matiasrg/FdD_Equipo_04/Proyecto/MóduloMecánico/vfinal/Bocetos/Boceto interior VFINAL.pdf

## BOCETO - EcoAlerta

Equipo 04 - Fundamentos de Diseño

DIBUJADO POR:
- Palacios Ochoa Jose Elias
- Jimenez Ayala Cielo Saori
- Espinoza Mayta Adriana
- Santos Almonte Jesilin

VISTA INTERNA:

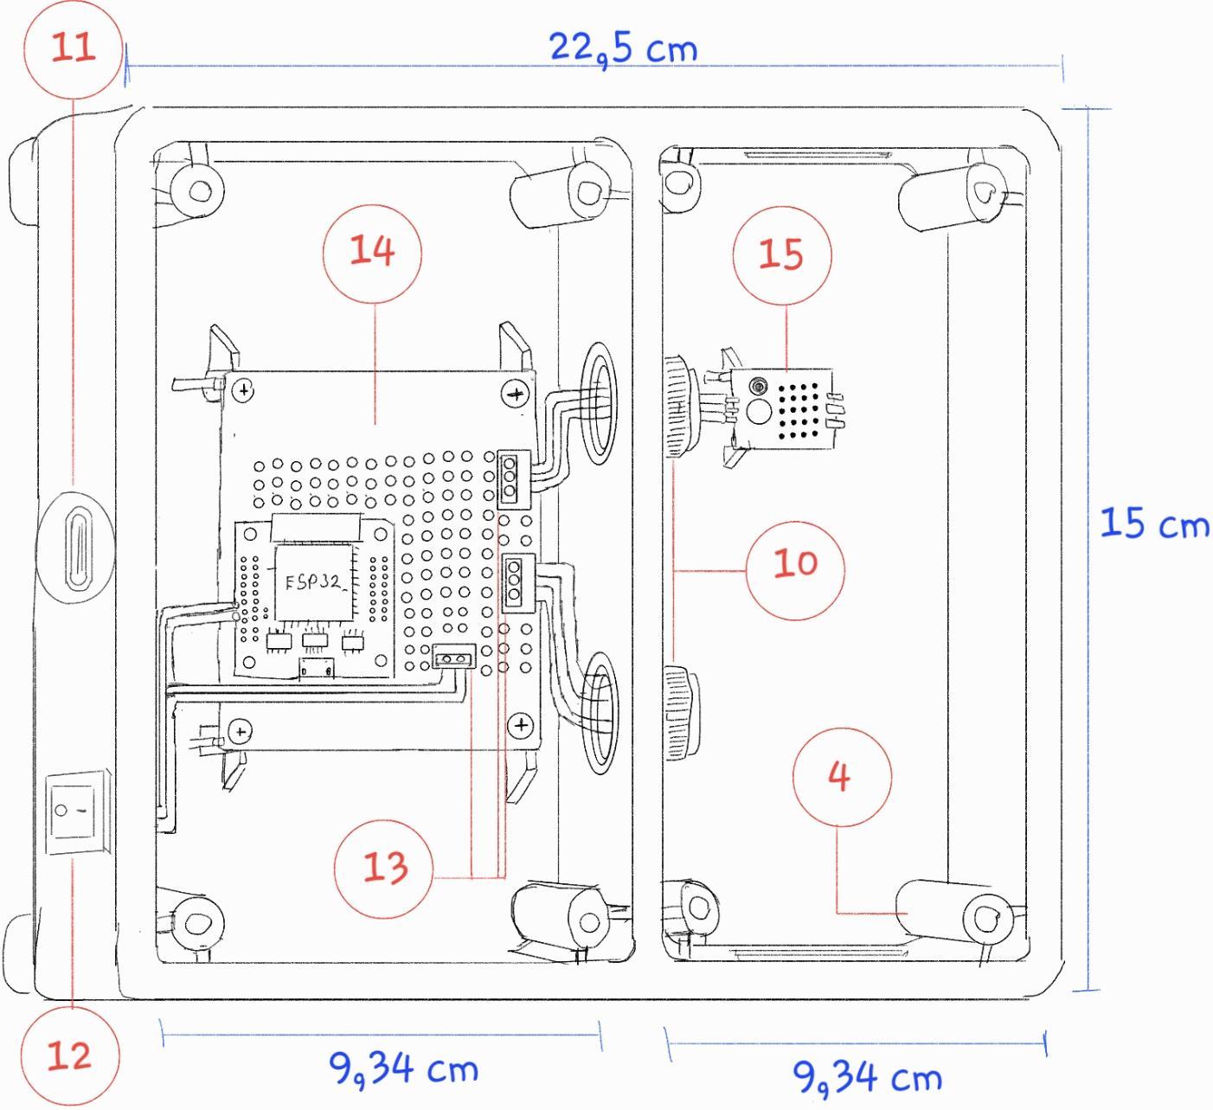
[picture p30: figure]

Descripción del funcionamiento: | LISTA DE DESPIECE:

La vista interna permite observar la organización de los componentes electrónicos dentro de la carcasa. Se identifican el

PIEZA | NOMBRE

microcontrolador ESP32, la bornera, el interruptor de encendido, el conector USB Tipo-C y los elementos de soporte que facilitan el montaje y
funcionamiento seguro del
sistema.
④ | Base/apoyo para tapa
⑩ | Prensaestopa PG7
⑪ | Conector USB Tipo-C hembra para montaje en panel
⑫ | Interruptor de encendido/apagado (ON/OFF)
⑬ | Bornera
⑭ | Microcontrolador ESP32 y placa perforada
⑮ | Sensor de temperatura y humedad (DHT22)
