matiasrg/FdD_Equipo_04/Proyecto/MóduloMecánico/vfinal/Bocetos/Boceto isométrico VFINAL.pdf

## BOCETO - EcoAlerta

Equipo 04 - Fundamentos de Diseño

DIBUJADO POR:
- Palacios Ochoa Jose Elias
- Jimenez Ayala Cielo Saori
- Espinoza Mayta Adriana
- Santos Almonte Jesilin
VISTA ISOMÉTRICA

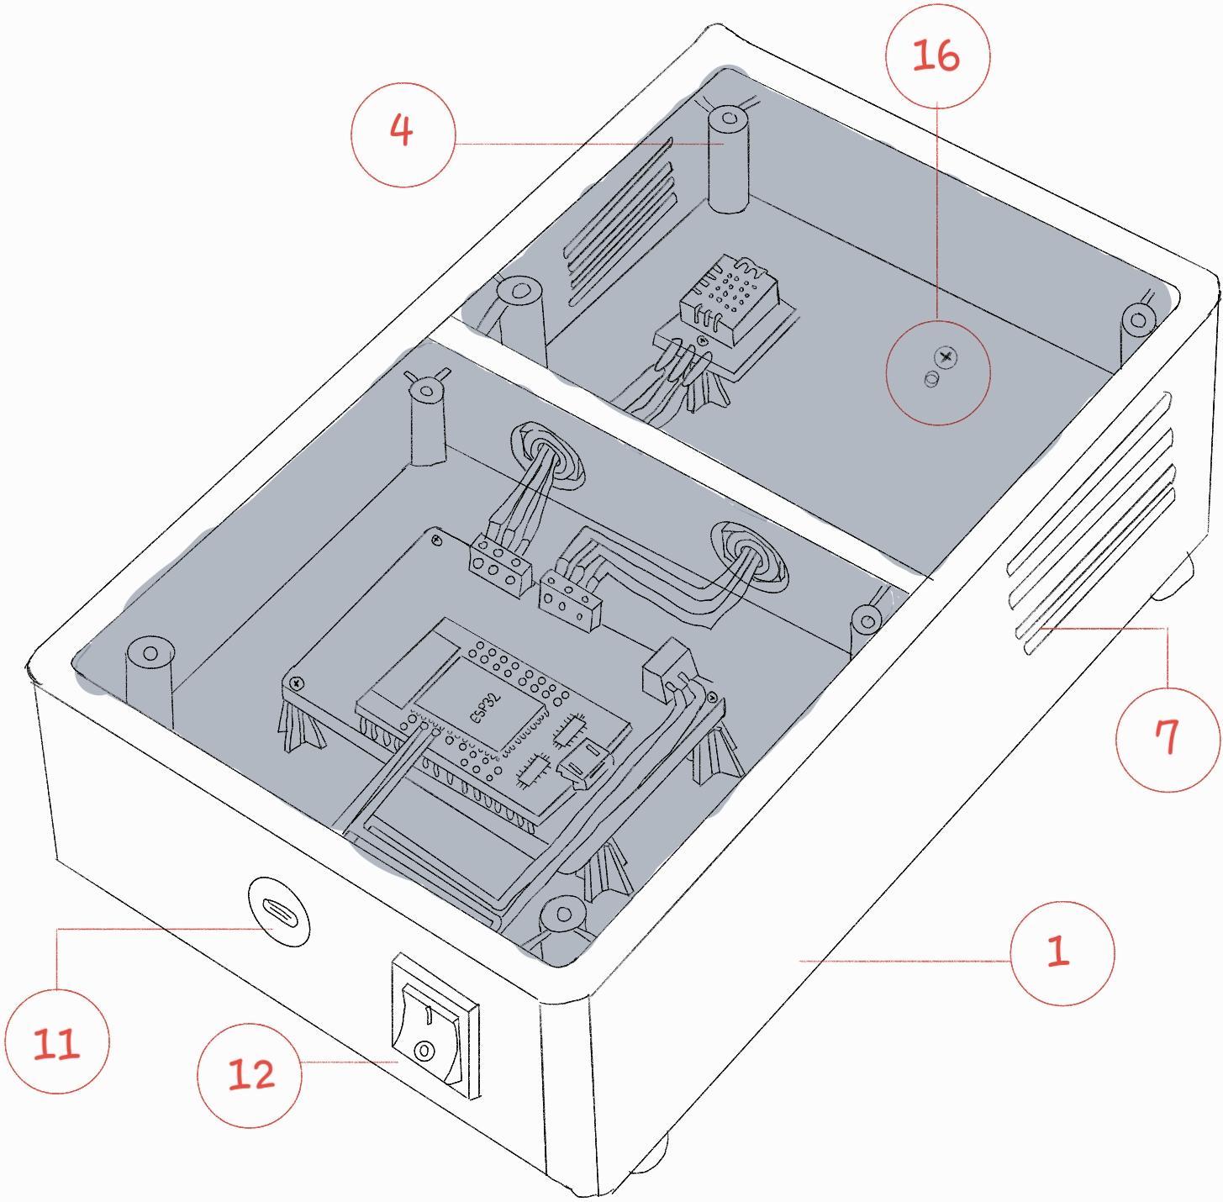
[picture p31: figure]

Descripción del funcionamiento: | LISTA DE DESPIECE:

La vista isométrica ofrece una representación tridimensional del dispositivo ensamblado, permitiendo visualizar

PIEZA | NOMBRE

simultáneamente varias caras de la estructura. Se aprecian la carcasa principal, las rejillas de ventilación, el sensor UV y los elementos de conexión externa, proporcionando una visión general del diseño final del producto.

① | Carcasa exterior rectangular (base)
④ | Base/apoyo para tapa
⑦ | Rejillas de ventilación lineales
⑪ | Conector USB Tipo-C hembra para montaje en panel
⑫ | Interruptor de encendido/apagado (ON/OFF)
⑯ | Sensor UV (UV SENS)
