matiasrg/FdD_Equipo_04/Proyecto/MóduloMecánico/vfinal/Bocetos/Boceto tapas VFINAL.pdf

## BOCETO - EcoAlerta

Equipo 04 - Fundamentos de Diseño

DIBUJADO POR:
- Palacios Ochoa Jose Elias
- Jimenez Ayala Cielo Saori
- Espinoza Mayta Adriana
- Santos Almonte Jesilin

VISTA DE TAPAS

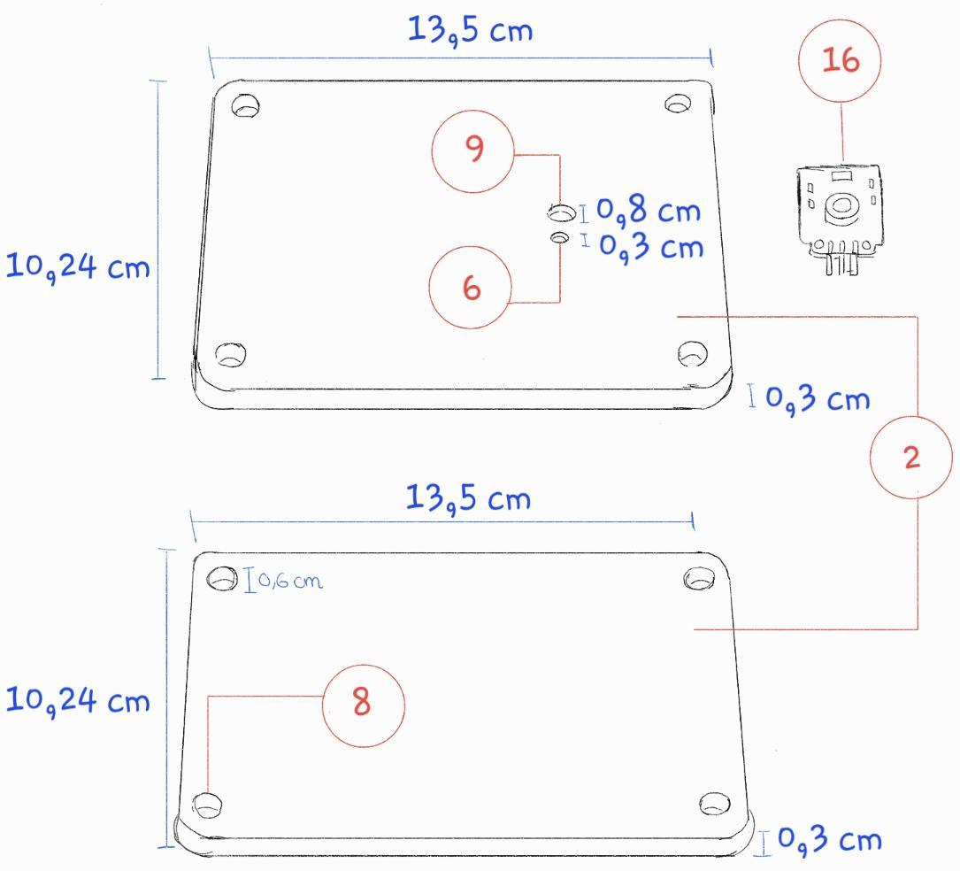
[picture p32: figure]

Descripción del funcionamiento: | LISTA DE DESPIECE:

Esta vista destaca la tapa superior del dispositivo y los elementos asociados a la medición de radiación ultravioleta. Se observa

PIEZA | NOMBRE

la abertura destinada al sensor UV junto con su soporte de fijación, así como los orificios para el ensamblaje mediante un tornillo que asegura la unión con la tapa y la carcasa que veremos más adelante.

② | Tapa protectora
⑥ | Apertura circular y soporte para sensor UV
⑧ | Hueco para tornillo
⑨ | Hueco para sensor UV
⑯ | Sensor UV (UV SENS)
