matiasrg/FdD_Equipo_04/Proyecto/MóduloMecánico/vfinal/Bocetos/Boceto conjunto VFINAL.pdf

## BOCETO - EcoAlerta

Equipo 04 - Fundamentos de Diseño

DIBUJADO POR:
- Palacios Ochoa Jose Elias
- Jimenez Ayala Cielo Saori
- Espinoza Mayta Adriana
- Santos Almonte Jesilin

BOCETO EN CONJUNTO

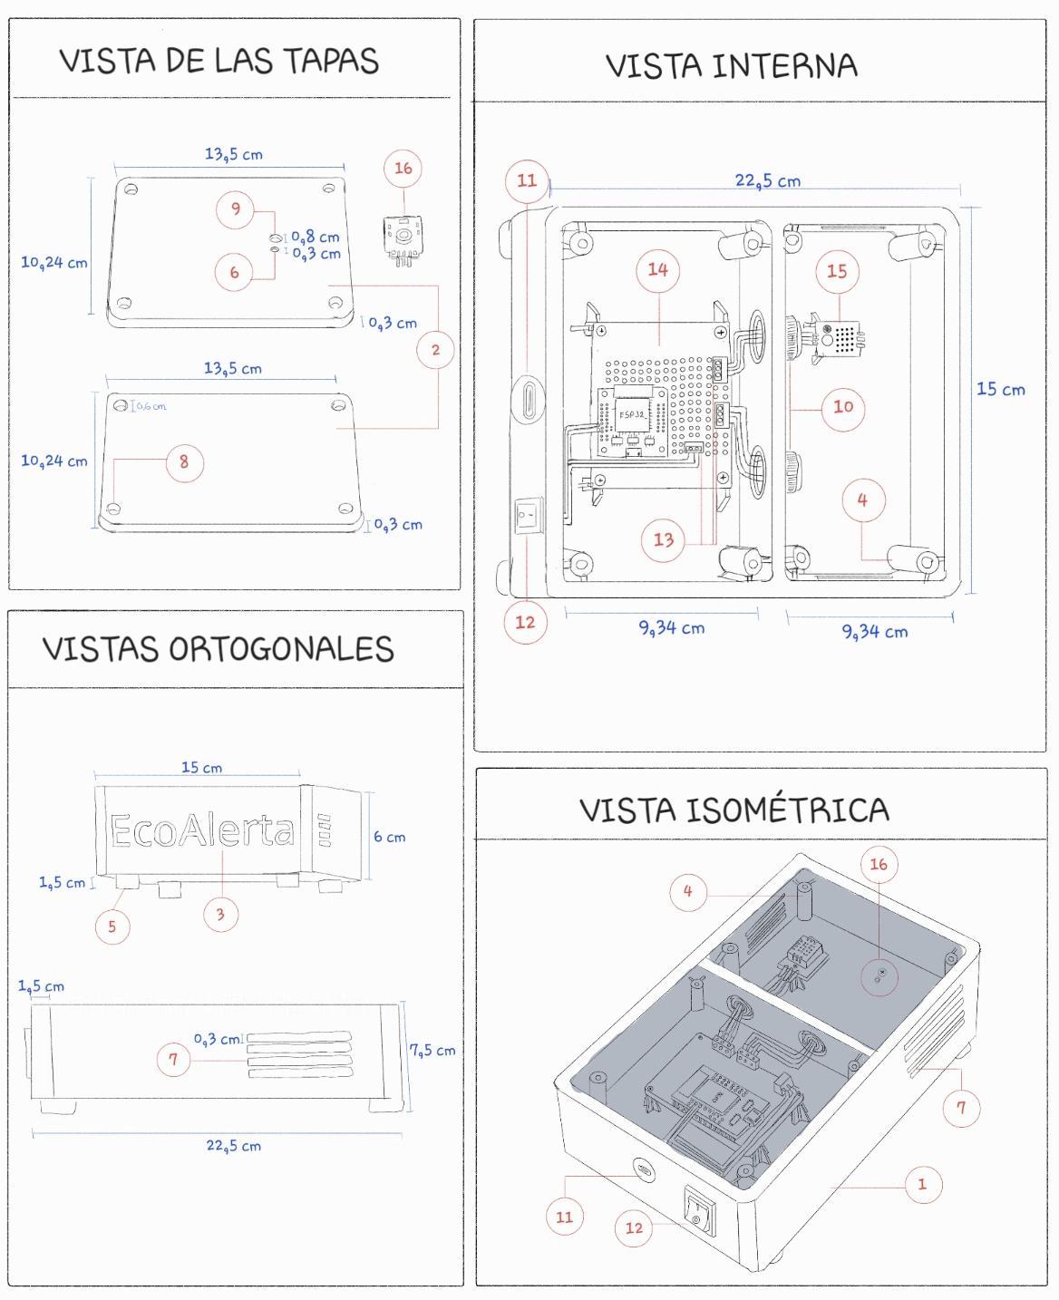
[picture p33: figure]

Descripción del funcionamiento: LISTA DE DESPIECE:

El dispositivo presenta una carcasa
rectangular compacta diseñada para
uso en exteriores. En la parte
superior se observan el sensor UV, colocado en una abertura circular para recibir directamente la radiación solar, y el sensor DHT22 junto a rejillas lineales que permiten la circulación de aire. En el interior se ubica el módulo ESP32 con las conexiones electrónicas, mientras que en el panel frontal se integran el puerto USB Tipo-C, el interruptor de encendido y el logotipo del proyecto EcoAlerta. El diseño busca facilitar tanto el monitoreo ambiental como el acceso para mantenimiento y alimentación eléctrica.
PIEZA | NOMBRE | MATERIAL
① | Carcasa exterior rectangular (base) | PETG
② | Tapa protectora | PETG
③ | Panel frontal con logo | PETG
④ | Base/apoyo para tapa | PETG
⑤ | Patitas | PETG
⑥ | Apertura circular y soporte para sensor UV | PETG
⑦ | Rejillas de ventilación lineales | PETG
⑧ | Hueco para tornillo | Integrado en la tapa
⑨ | Hueco para sensor UV | Integrado en la tapa
⑩ | Prensaestopa PG7 | Nylon (PA66)
⑪ | Conector USB Tipo-C hembra para montaje en panel | Componente electrónico
⑫ | Interruptor de encendido/apagado (ON/OFF) | Componente electrónico
⑬ | Bornera | Componente electrónico
⑭ | Microcontrolador ESP32 y placa perforada | Componentes electrónicos
⑮ | Sensor de temperatura y humedad (DHT22) | Componente electrónico
⑯ | Sensor UV (UV SENS) | Componente electrónico
