matiasrg/FdD_Equipo_04/Proyecto/MóduloMecánico/Certificados/Jose Palacios/Jose Palacios.pdf

JOSE ELIAS PALACIOS OCHOA

Advanced Onshape Assemblies

May 21, 2026

JOSE ELIAS PALACIOS OCHOA

April 29, 2026

Introduction to Onshape Assemblies

JOSE ELIAS PALACIOS OCHOA

April 29, 2026

Detailed Drawings

JOSE ELIAS PALACIOS OCHOA

April 30, 2026

Introduction to Drawings

JOSE ELIAS PALACIOS OCHOA

Introduction to Part Studios

April 29, 2026

JOSE ELIAS PALACIOS OCHOA

Introduction to Sketching

April 29, 2026
