matiasrg/FdD_Equipo_04/Proyecto/MóduloMecánico/Certificados/Adriana Espinoza/Adriana Espinoza.pdf

Adriana Anghely Espinoza Mayta

Advanced Onshape Assemblies

May 21, 2026

Adriana Anghely Espinoza Mayta

April 30, 2026

Detailed Drawings

Adriana Anghely Espinoza Mayta

April 30, 2026

Introduction to Drawings

Adriana Anghely Espinoza Mayta

April 30, 2026

Introduction to Onshape Assemblies

Adriana Anghely Espinoza Mayta

Introduction to Part Studios

April 30, 2026

Adriana Anghely Espinoza Mayta

Introduction to Sketching

April 30, 2026
