matiasrg/FdD_Equipo_04/Proyecto/MóduloMecánico/Certificados/Cielo Jiménez/Saori Jimenez.pdf

Cielo Saori Jimenez Ayala

Advanced Onshape Assemblies

May 21, 2026

Cielo Saori Jimenez Ayala

April 30, 2026

Detailed Drawings

Cielo Saori Jimenez Ayala

April 30, 2026

Introduction to Drawings

Cielo Saori Jimenez Ayala

April 30, 2026

Introduction to Onshape Assemblies

Cielo Saori Jimenez Ayala

Introduction to Part Studios

April 30, 2026

Cielo Saori Jimenez Ayala

Introduction to Sketching

April 30, 2026
