matiasrg/FdD_Equipo_04/Proyecto/MóduloMecánico/Certificados/Jesilin Santos/Jesilin Santos.pdf

Jesilin Santos Almonte

Advanced Onshape Assemblies

May 21, 2026

Jesilin Santos Almonte

April 29, 2026

Detailed Drawings

Jesilin Santos Almonte

April 30, 2026

Introduction to Drawings

Jesilin Santos Almonte

April 29, 2026

Introduction to Onshape Assemblies

Jesilin Santos Almonte

Introduction to Part Studios

April 29, 2026

Jesilin Santos Almonte

Introduction to Sketching

April 29, 2026
