matiasrg/FdD_Equipo_04/Proyecto/MóduloMecánico/Certificados/Matias Rivera/Matias Rivera.pdf

Matias Rivera

Advanced Onshape Assemblies

May 21, 2026

MatiasR Rivera

April 30, 2026

Detailed Drawings

MatiasR Rivera

April 30, 2026

Introduction to Drawings

MatiasR Rivera

April 30, 2026

Introduction to Onshape Assemblies

MatiasR Rivera

Introduction to Part Studios

April 30, 2026

MatiasR Rivera

Introduction to Sketching

April 30, 2026
