matiasrg/FdD_Equipo_04/FundDiseño/Talleres/Taller_04/Taller_04.md

# LISTA DE PATENTES:

1. **UV light monitoring system for a UV decontamination apparatus**
   -Resumen: Esta patente describe un sistema de monitoreo de luz ultravioleta (UV) aplicado a dispositivos de desinfección. El sistema es capaz de estimar con precisión la irradiancia UV que recibe una superficie, incluso cuando esta se encuentra en diferentes ángulos respecto a la fuente de luz UV.
   <br>
   -Código: US12409241B2
   <br>
   -link: https://worldwide.espacenet.com/patent/search/family/073196745/publication/US12409241B2?q=pn%3DUS12409241B2
   <br>
   -Imagen:
   <br>
   <div align="center">
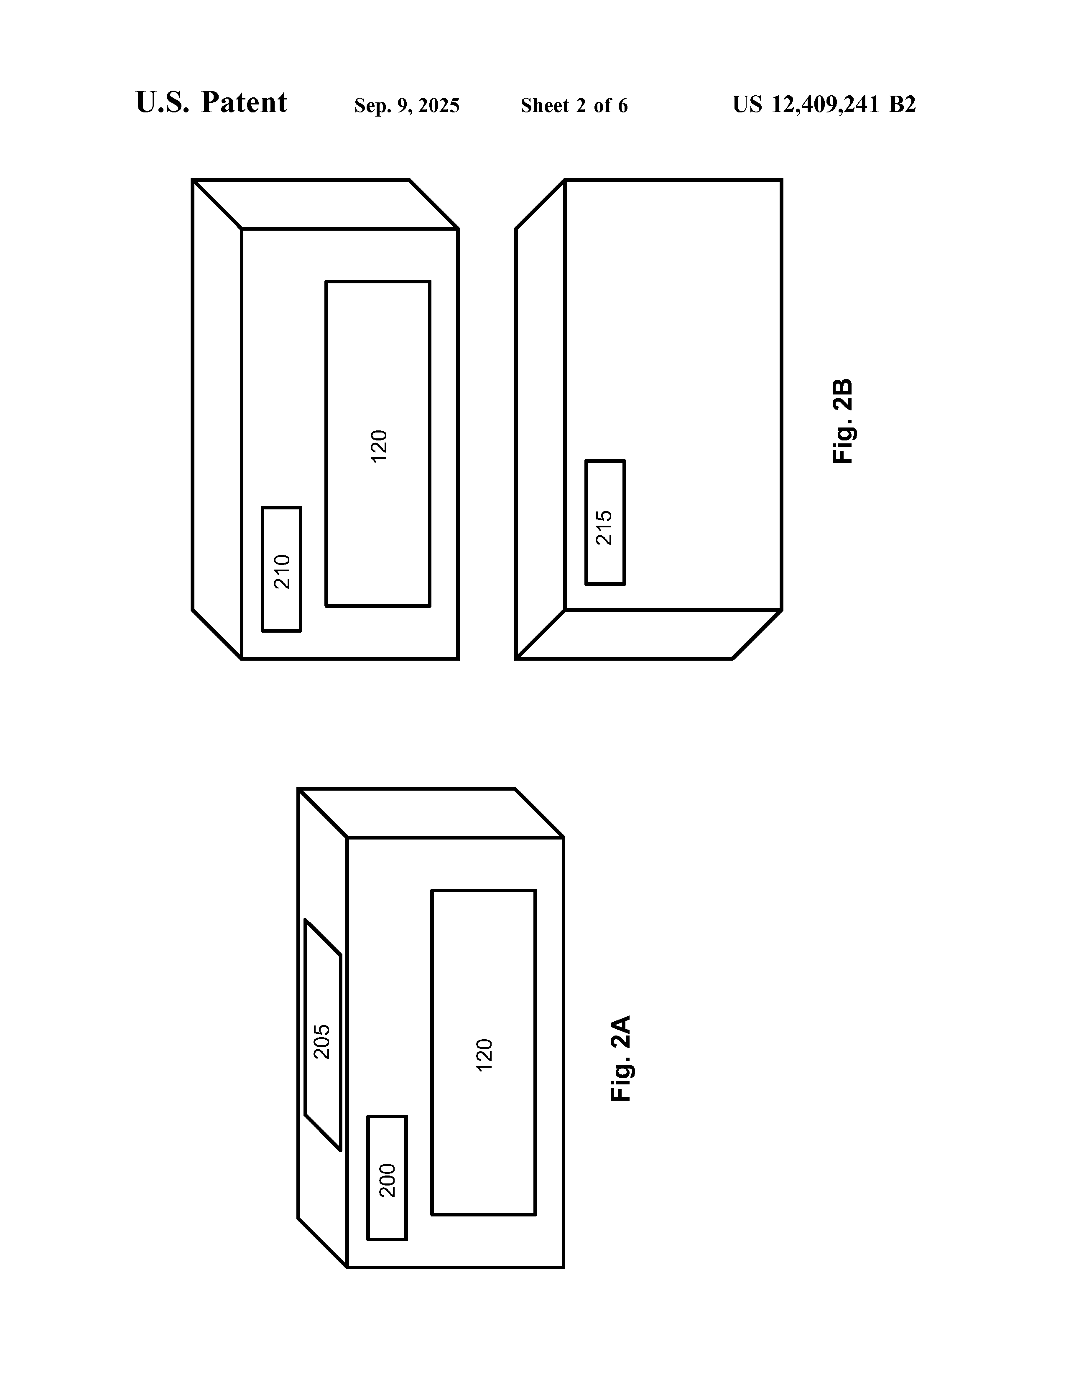
[picture p34: Recursos/Imágenes/patente1.png]
      
   </div>
   <br>
2. **Sistema de gestión de inventarios basado en inteligencia artificial para monitorear la disponibilidad de productos mediante datos IoT**
   (KI-gestütztes Bestandsverwaltungssystem zur Überwachung der Produktverfügbarkeit mithilfe von IoT-Daten)
   
  -Resumen: Esta patente describe un sistema de gestión de inventarios basado en Internet de las Cosas (IoT) e inteligencia artificial (IA), diseñado para monitorear la disponibilidad de productos en tiempo real dentro de entornos como almacenes o tiendas
  <br>
  -Código: DE202025101045U1
  <br>
  -Link: https://worldwide.espacenet.com/patent/search/family/095158102/publication/DE202025101045U1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
  <br>
  -Imagen:
  <br>
   <div align="center">
      
   </div>

3. **Sistema, dispositivo y métodos para el seguimiento de la exposición a la luz**
    (Light exposure tracking system, device, and methods)
   -Resumen: La patente describe un sistema portátil (wearable) que mide la exposición a la radiación UV en tiempo real. El dispositivo recopila datos y los envía a un sistema externo que calcula el índice UV y la dosis acumulada diaria, ayudando a prevenir riesgos para la salud
   <br>
   -Código: US11579015B2
   <br>
   -Link: https://worldwide.espacenet.com/patent/search/family/065362927/publication/US11579015B2?q=pn%3DUS11579015B2
   <br>
   -Imágen:
    <div align="center">
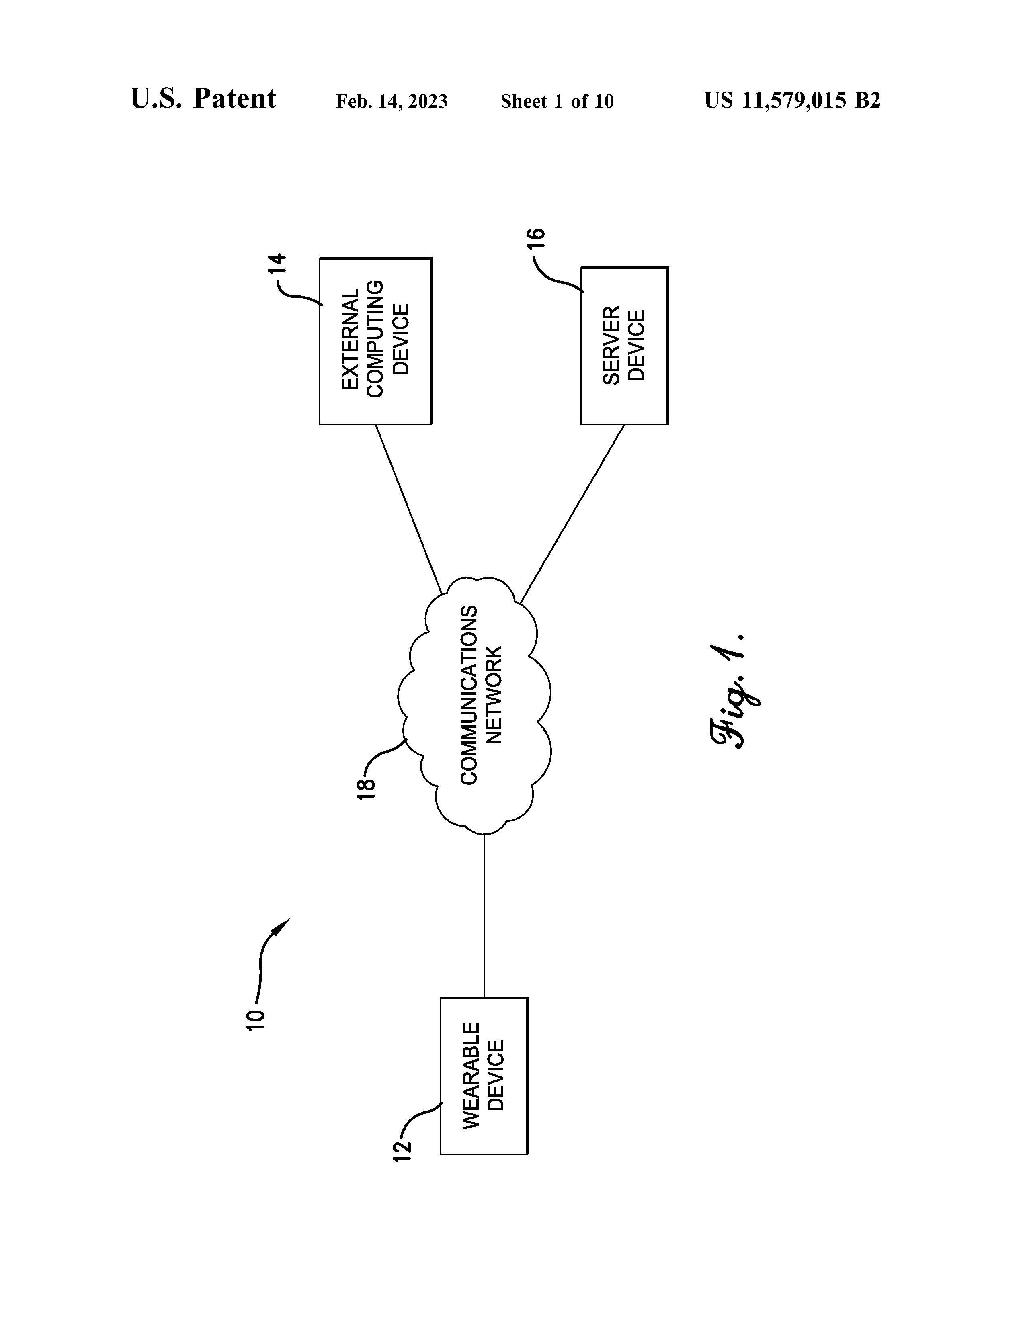
[picture p35: Recursos/Imágenes/patente3.png]
      
   </div>
