matiasrg/FdD_Equipo_04/FundDiseño/Talleres/taller_10/onshape/Imagen - Modelado 3D.pdf

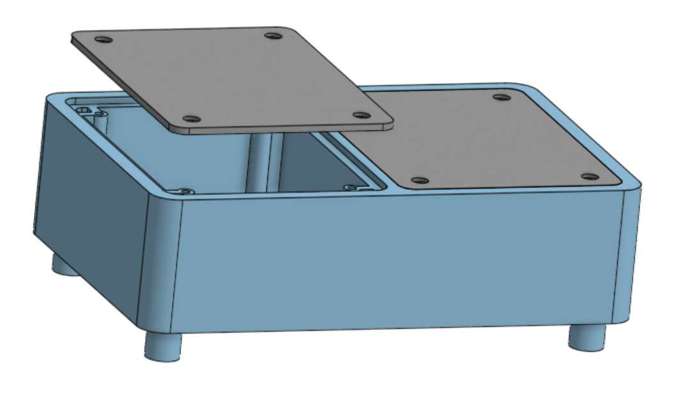
[picture p38: page 1]
