matiasrg/FdD_Equipo_04/Recursos/Productos comerciales/Brochure producto 2.pdf

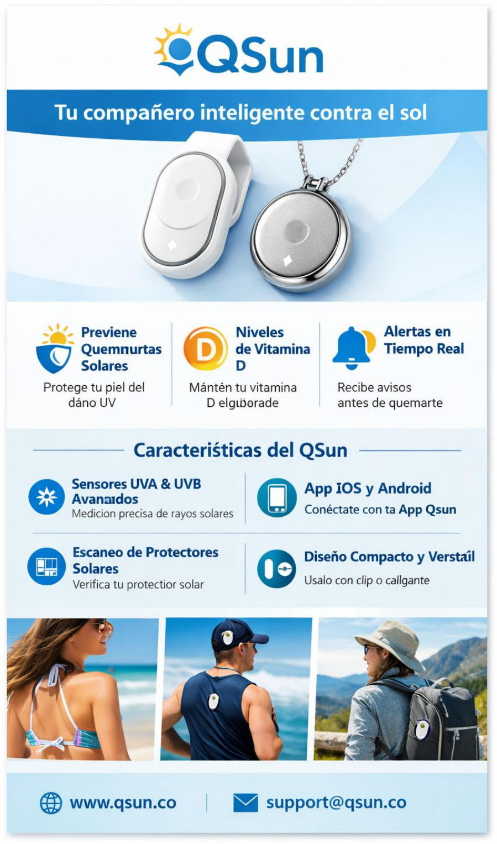
[picture p39: page 1]
