matiasrg/FdD_Equipo_04/Proyecto/MóduloMecánico/vfinal/Bocetos/Boceto Frontal y Lateral VFINAL.pdf

## BOCETO - EcoAlerta

Equipo 04 - Fundamentos de Diseño

DIBUJADO POR:
- Palacios Ochoa Jose Elias
- Jimenez Ayala Cielo Saori
- Espinoza Mayta Adriana
- Santos Almonte Jesilin

VISTAS ORTOGONALES

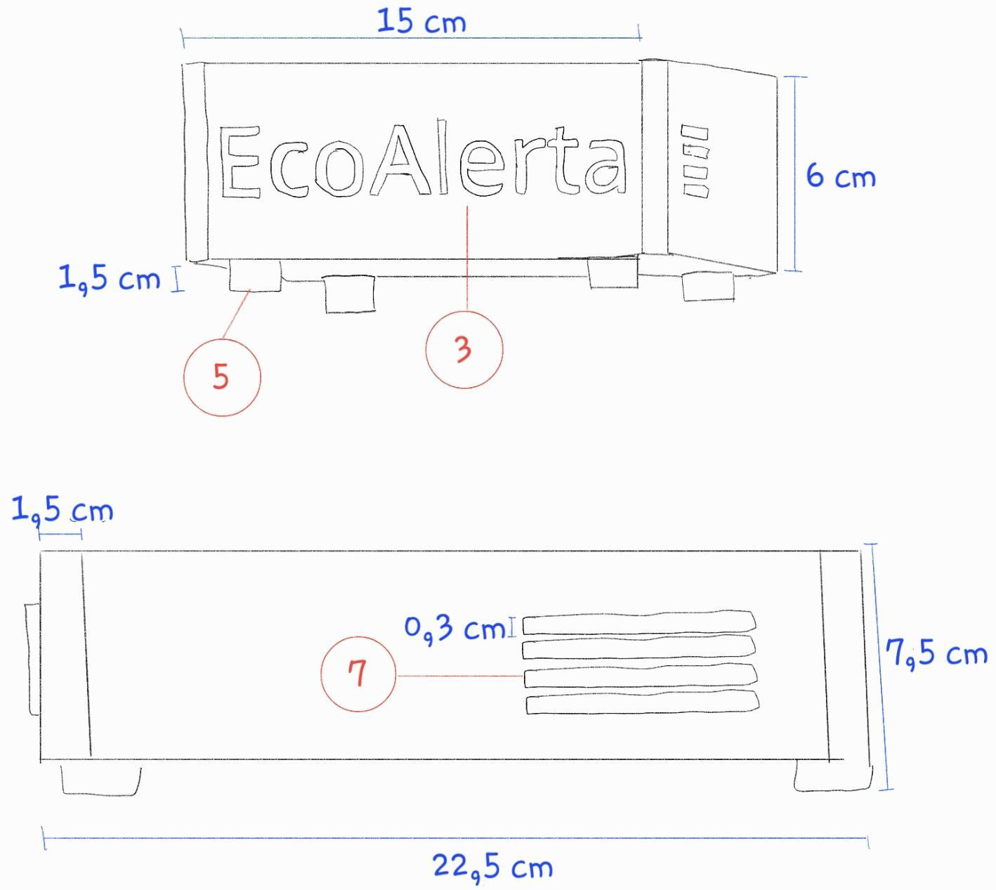
[picture p40: figure]

Descripción del funcionamiento: | LISTA DE DESPIECE:

Las vistas ortogonales presentan el dispositivo desde diferentes perspectivas, permitiendo apreciar con mayor claridad su forma,

PIEZA | NOMBRE

dimensiones y distribución exterior. En ellas destacan las rejillas de ventilación, el panel frontal con el logotipo del proyecto y las patitas de apoyo que proporcionan estabilidad al conjunto.

③ | Panel frontal con logo ⑤ | Patitas ⑦ | Rejillas de ventilación lineales
