matiasrg/FdD_Equipo_04/Proyecto/MóduloMecánico/v1/Onshape/Partes/Part Studio 3 - Part 12.stl

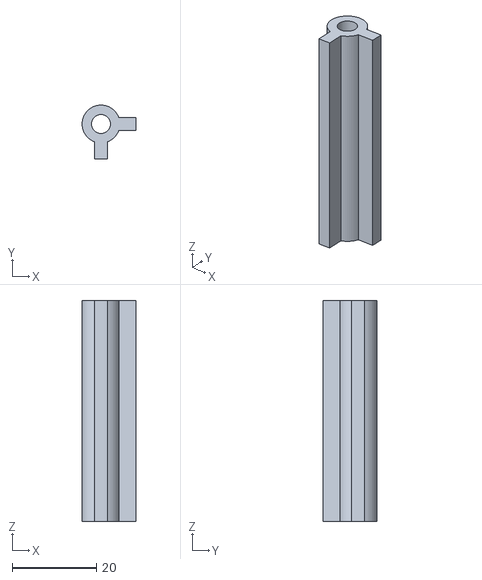
[picture p59: CAD file, 2026-05-28]
Proyecto/MóduloMecánico/v1/Onshape/Partes/Part Studio 3 - Part 12.stl
12.8 x 12.8 x 52.5
