matiasrg/FdD_Equipo_04/Proyecto/MóduloMecánico/v1/Onshape/Partes/Part Studio 3 - Part 4.stl

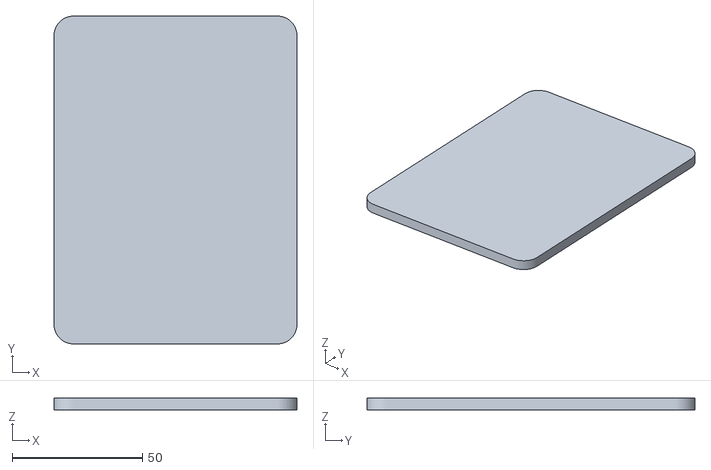
[picture p60: CAD file, 2026-05-28]
Proyecto/MóduloMecánico/v1/Onshape/Partes/Part Studio 3 - Part 4.stl
93.4 x 126.0 x 4.50
