matiasrg/FdD_Equipo_04/Proyecto/MóduloMecánico/v1/Onshape/Partes/Part Studio 3 - Part 23.stl

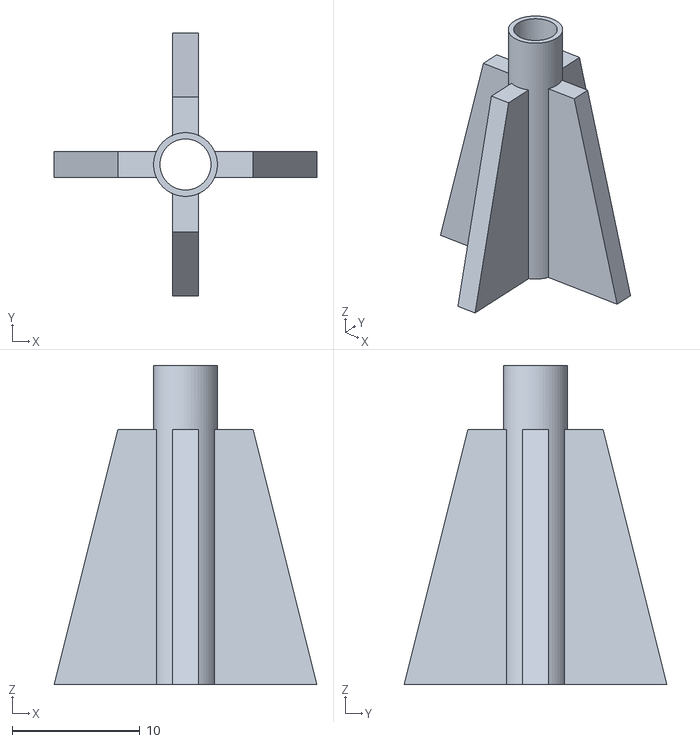
[picture p61: CAD file, 2026-05-28]
Proyecto/MóduloMecánico/v1/Onshape/Partes/Part Studio 3 - Part 23.stl
20.6 x 20.6 x 25.0
