matiasrg/FdD_Equipo_04/Proyecto/MóduloMecánico/v1/Onshape/Partes/Part Studio 3 - Part 2.stl

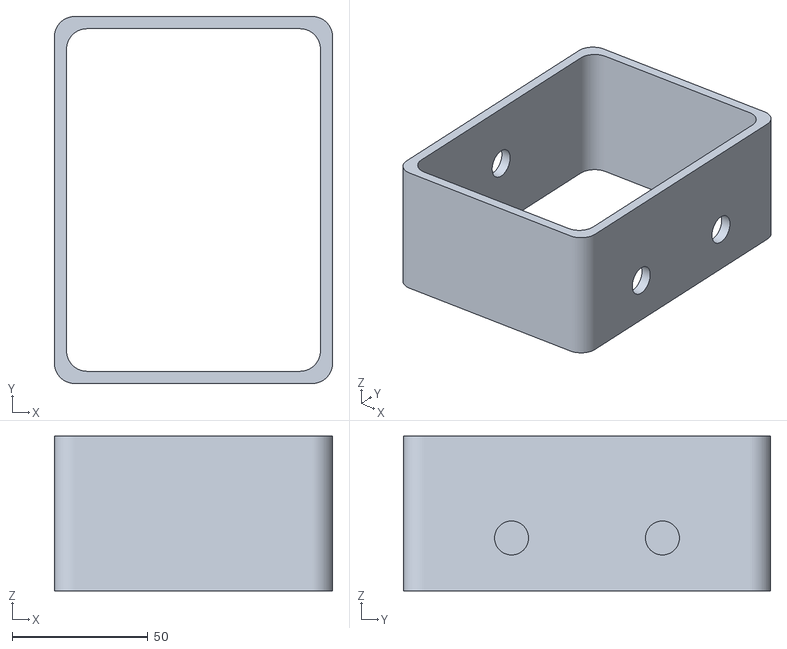
[picture p62: CAD file, 2026-05-28]
Proyecto/MóduloMecánico/v1/Onshape/Partes/Part Studio 3 - Part 2.stl
102.4 x 135.0 x 57.0
