matiasrg/FdD_Equipo_04/Proyecto/MóduloMecánico/v1/Onshape/Partes/tapa1.stl

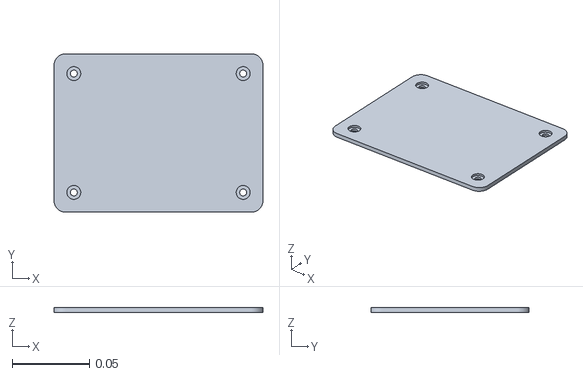
[picture p63: CAD file, 2026-05-28]
Proyecto/MóduloMecánico/v1/Onshape/Partes/tapa1.stl
0.135 x 0.102 x 0.003
