matiasrg/FdD_Equipo_04/Proyecto/MóduloElectrónico/V4.0/V4.0.pdf

Alimentación | Microcontrolador

# Sensor de

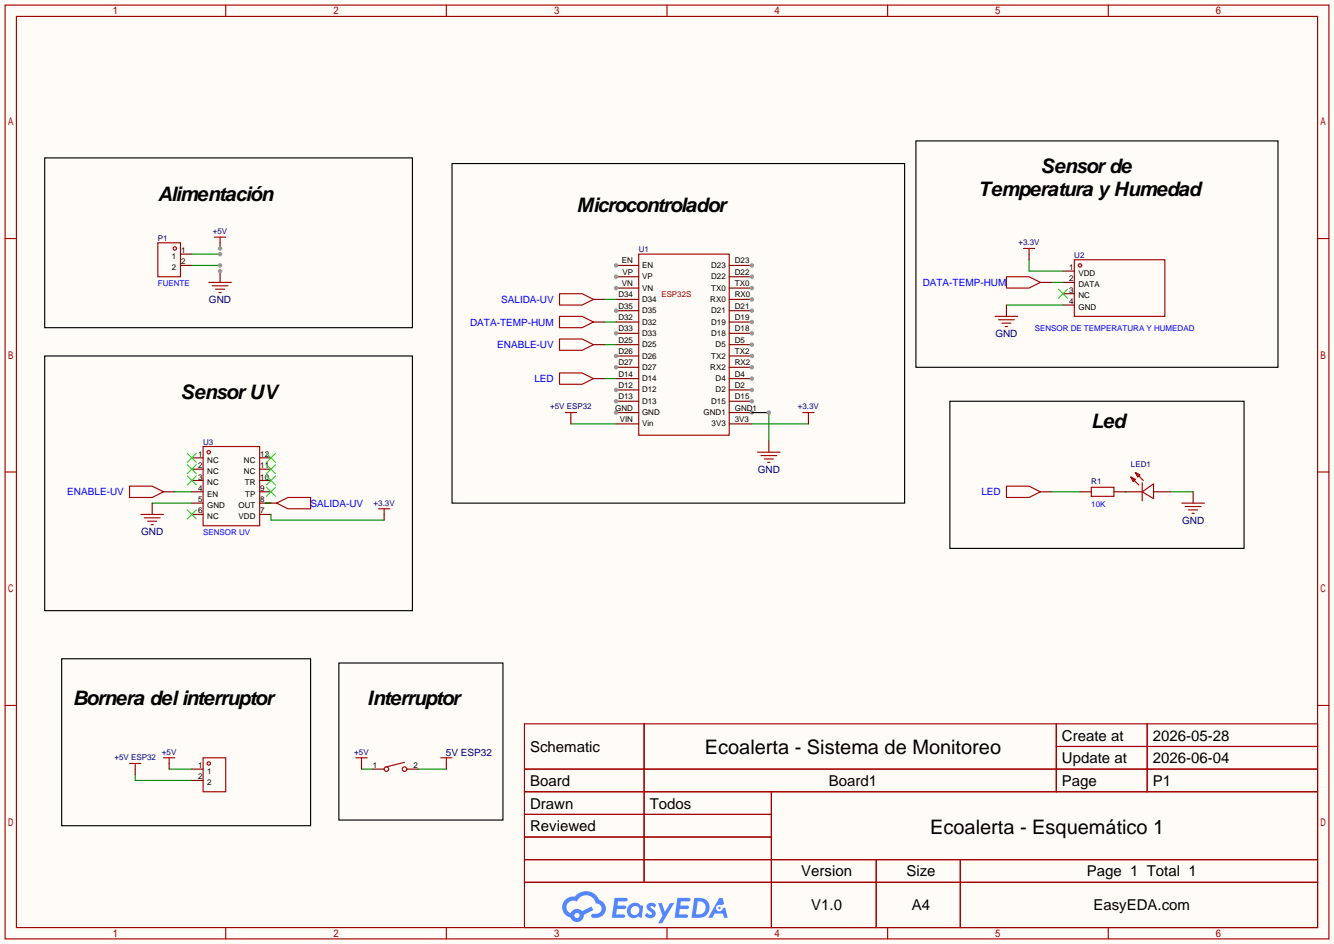
[picture p68: page 1]

SENSOR DE TEMPERATURA Y HUMEDAD
GND

Schematic | Ecoalerta - Sistema de Monitoreo | Create at | 2026-05-28

Update at | 2026-06-04

Board | Board1 | Page | P1
Drawn | Todos | Ecoalerta - Esquemático 1
Reviewed

Version | Size | Page 1 Total 1
V1.0 | A4 | EasyEDA.com
