matiasrg/FdD_Equipo_04/Proyecto/MóduloMecánico/vfinal/Oneshape/Planos/Contenedor.pdf

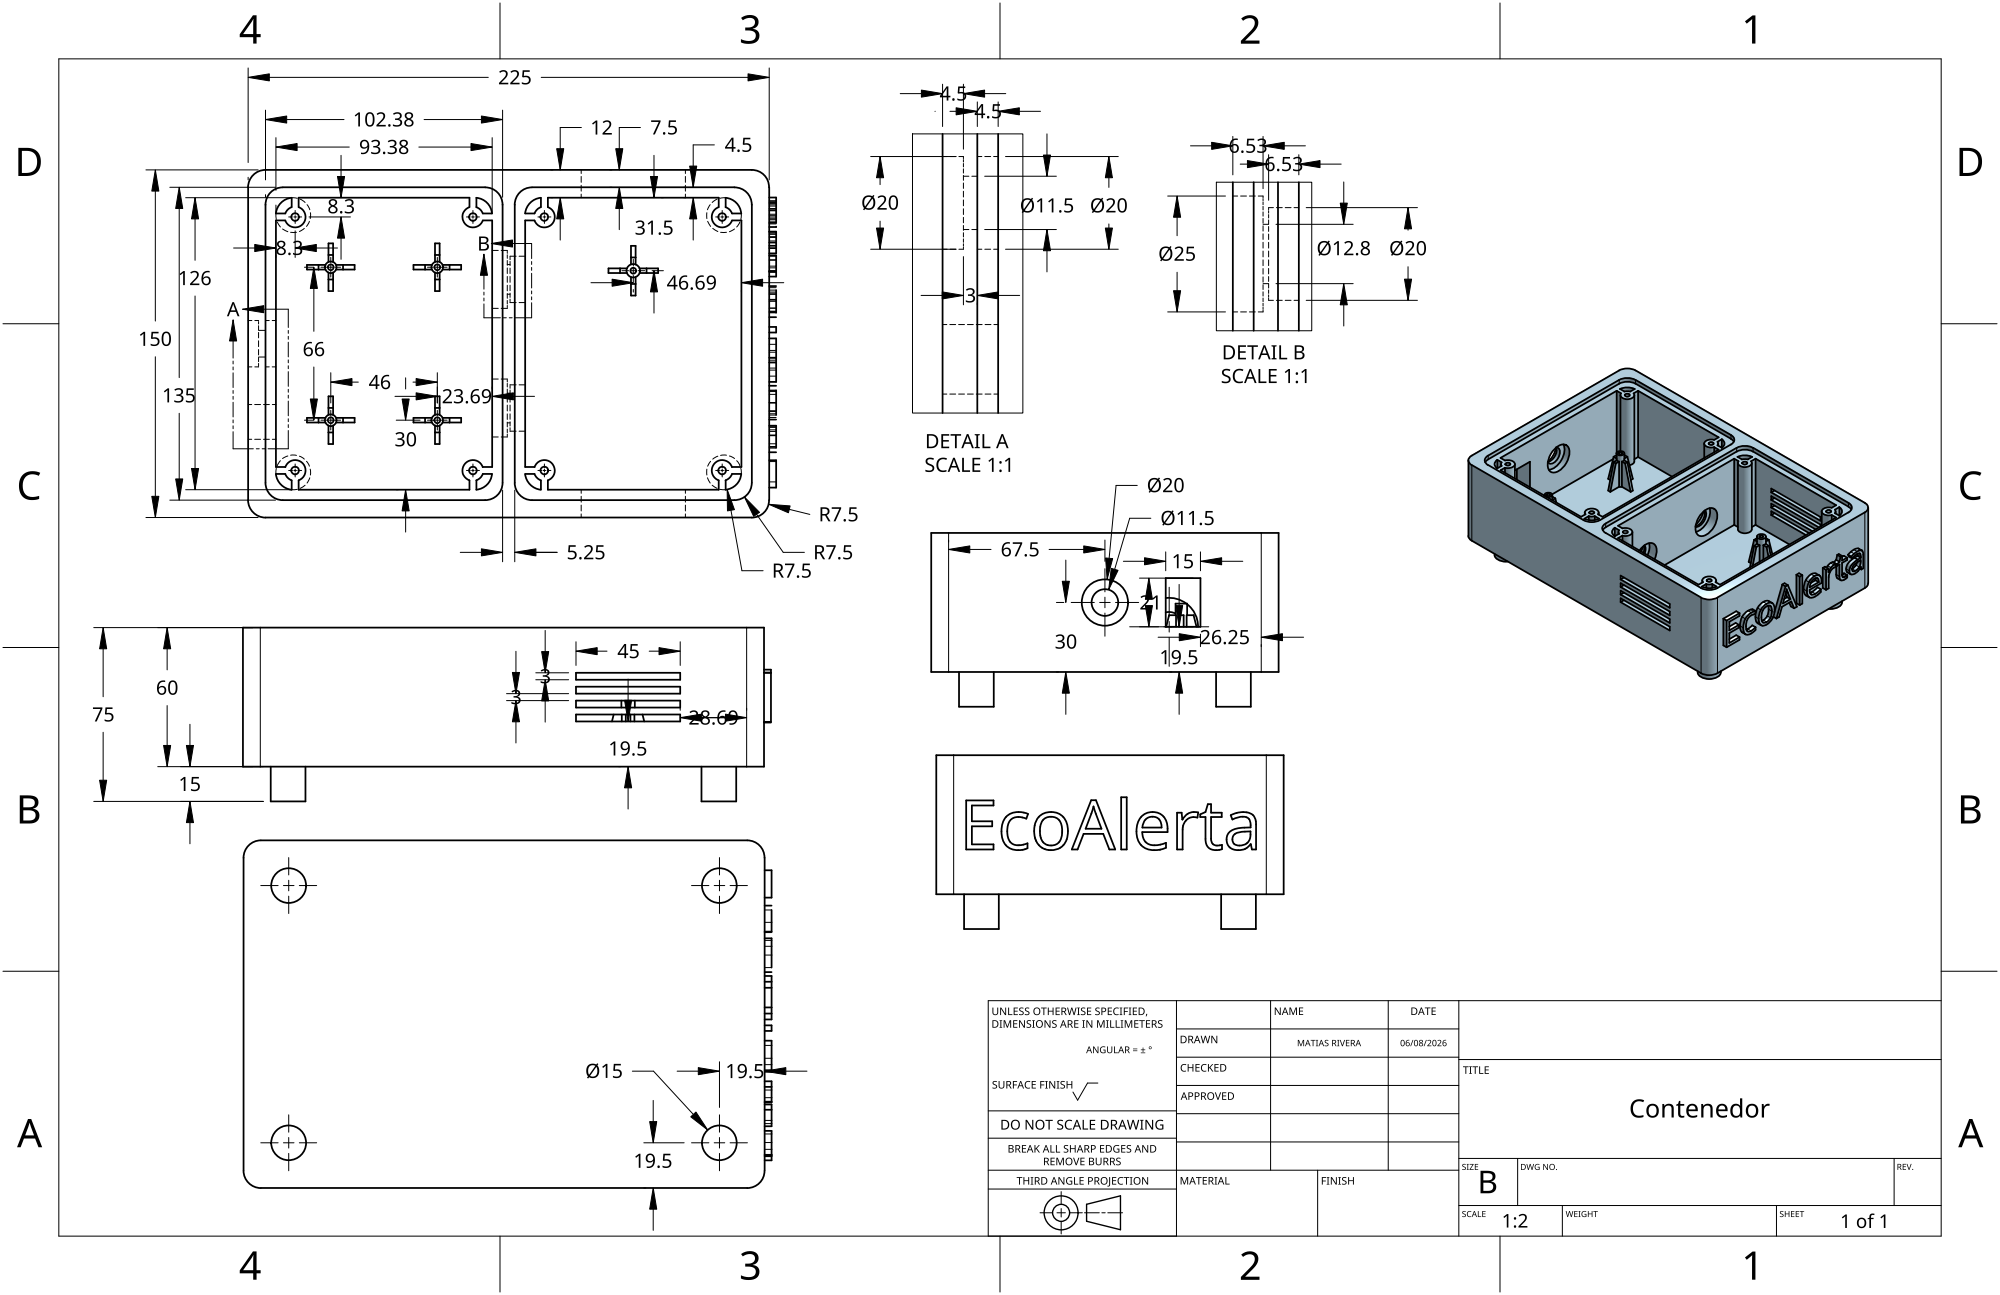
[picture p71: page 1]
