matiasrg/FdD_Equipo_04/Proyecto/MóduloMecánico/vfinal/Oneshape/Planos/Fijador de DHT11.pdf

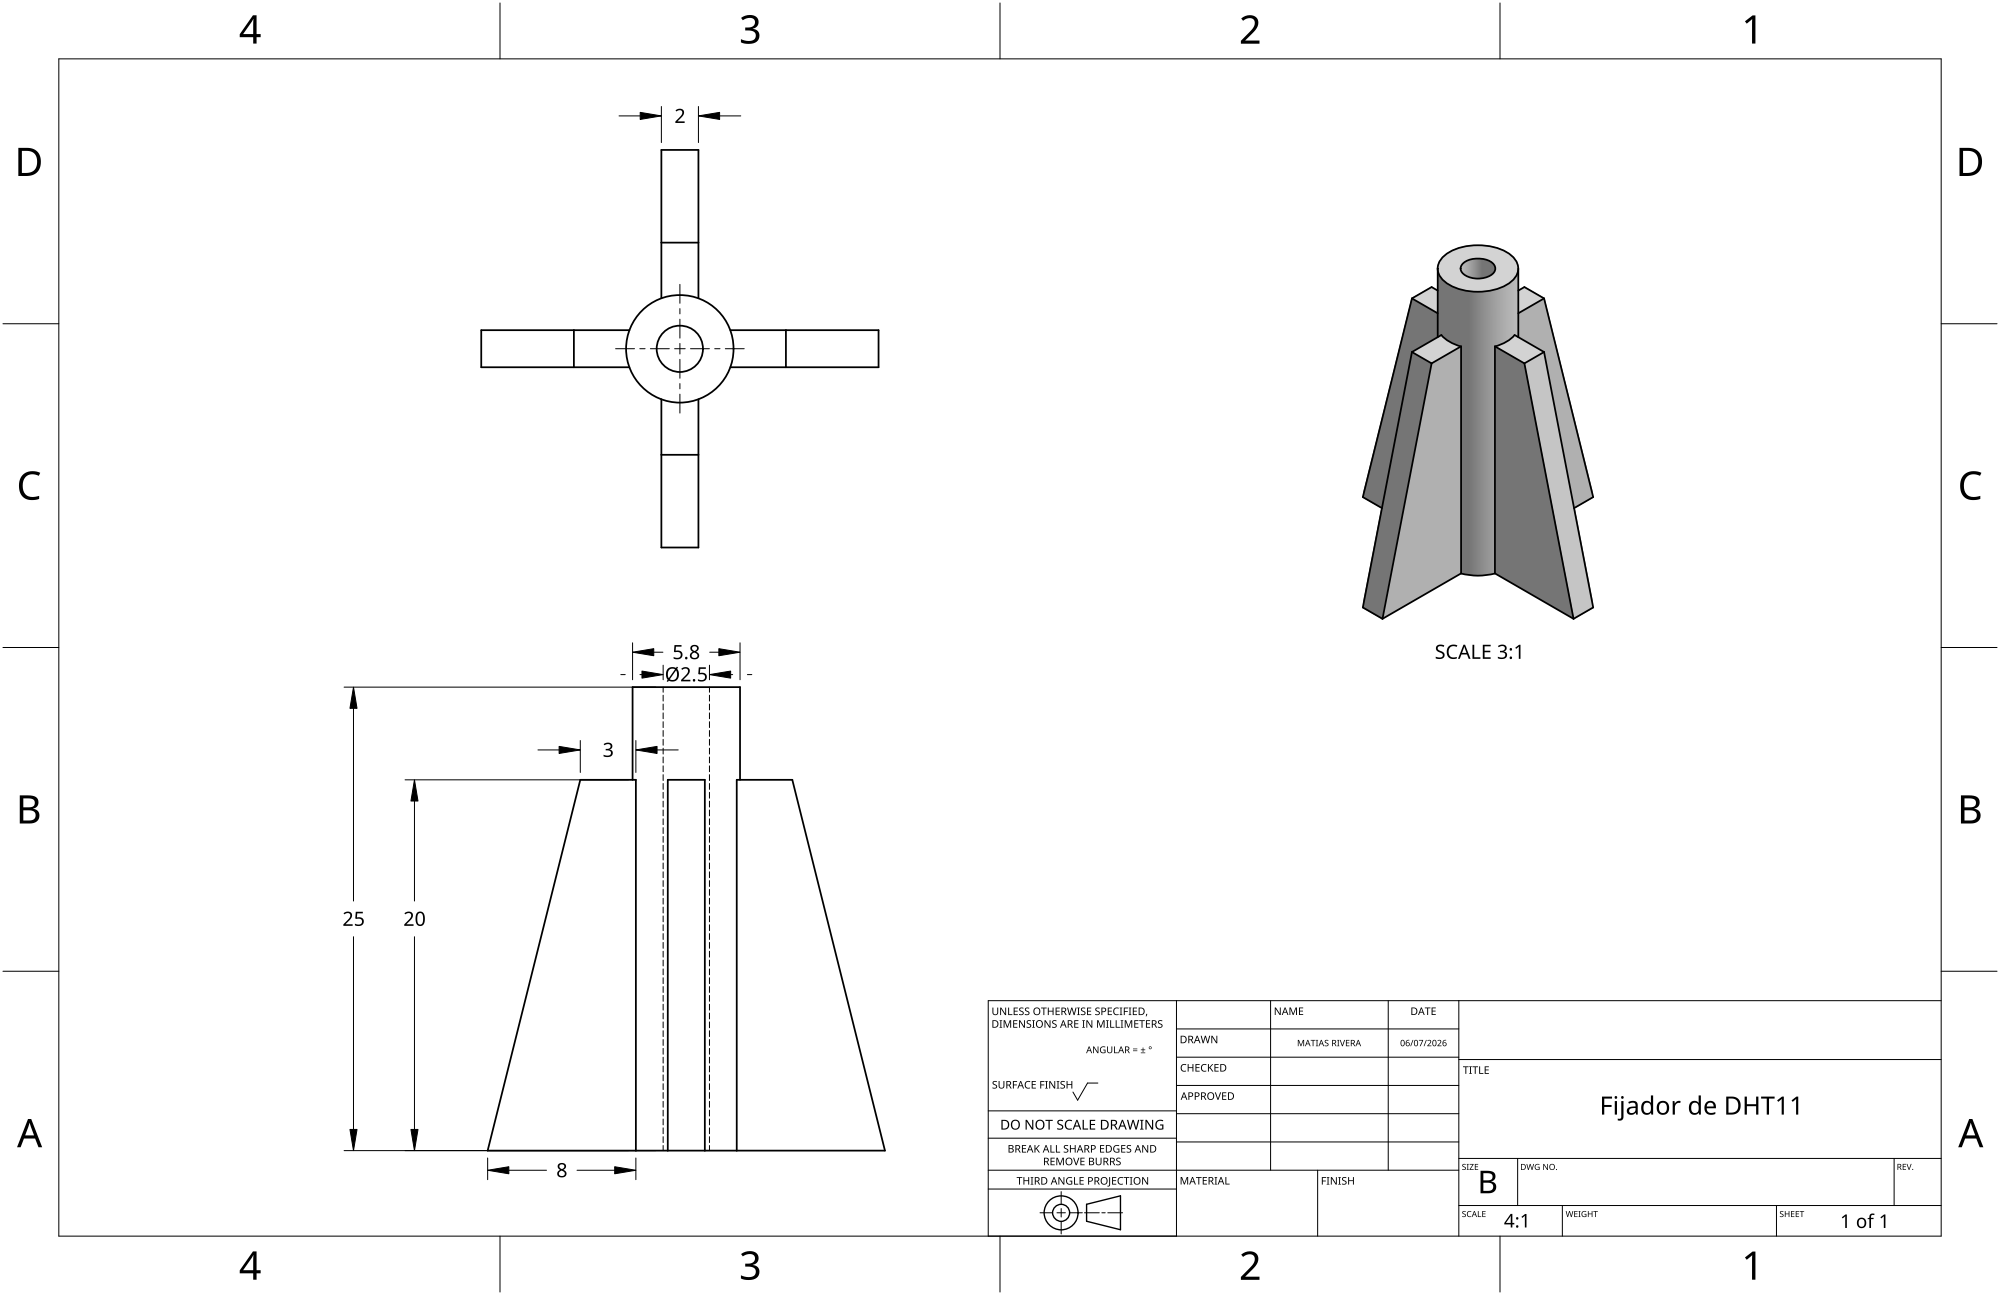
[picture p72: page 1]
