matiasrg/FdD_Equipo_04/Proyecto/MóduloMecánico/vfinal/Oneshape/Planos/Fijador de la placa.pdf

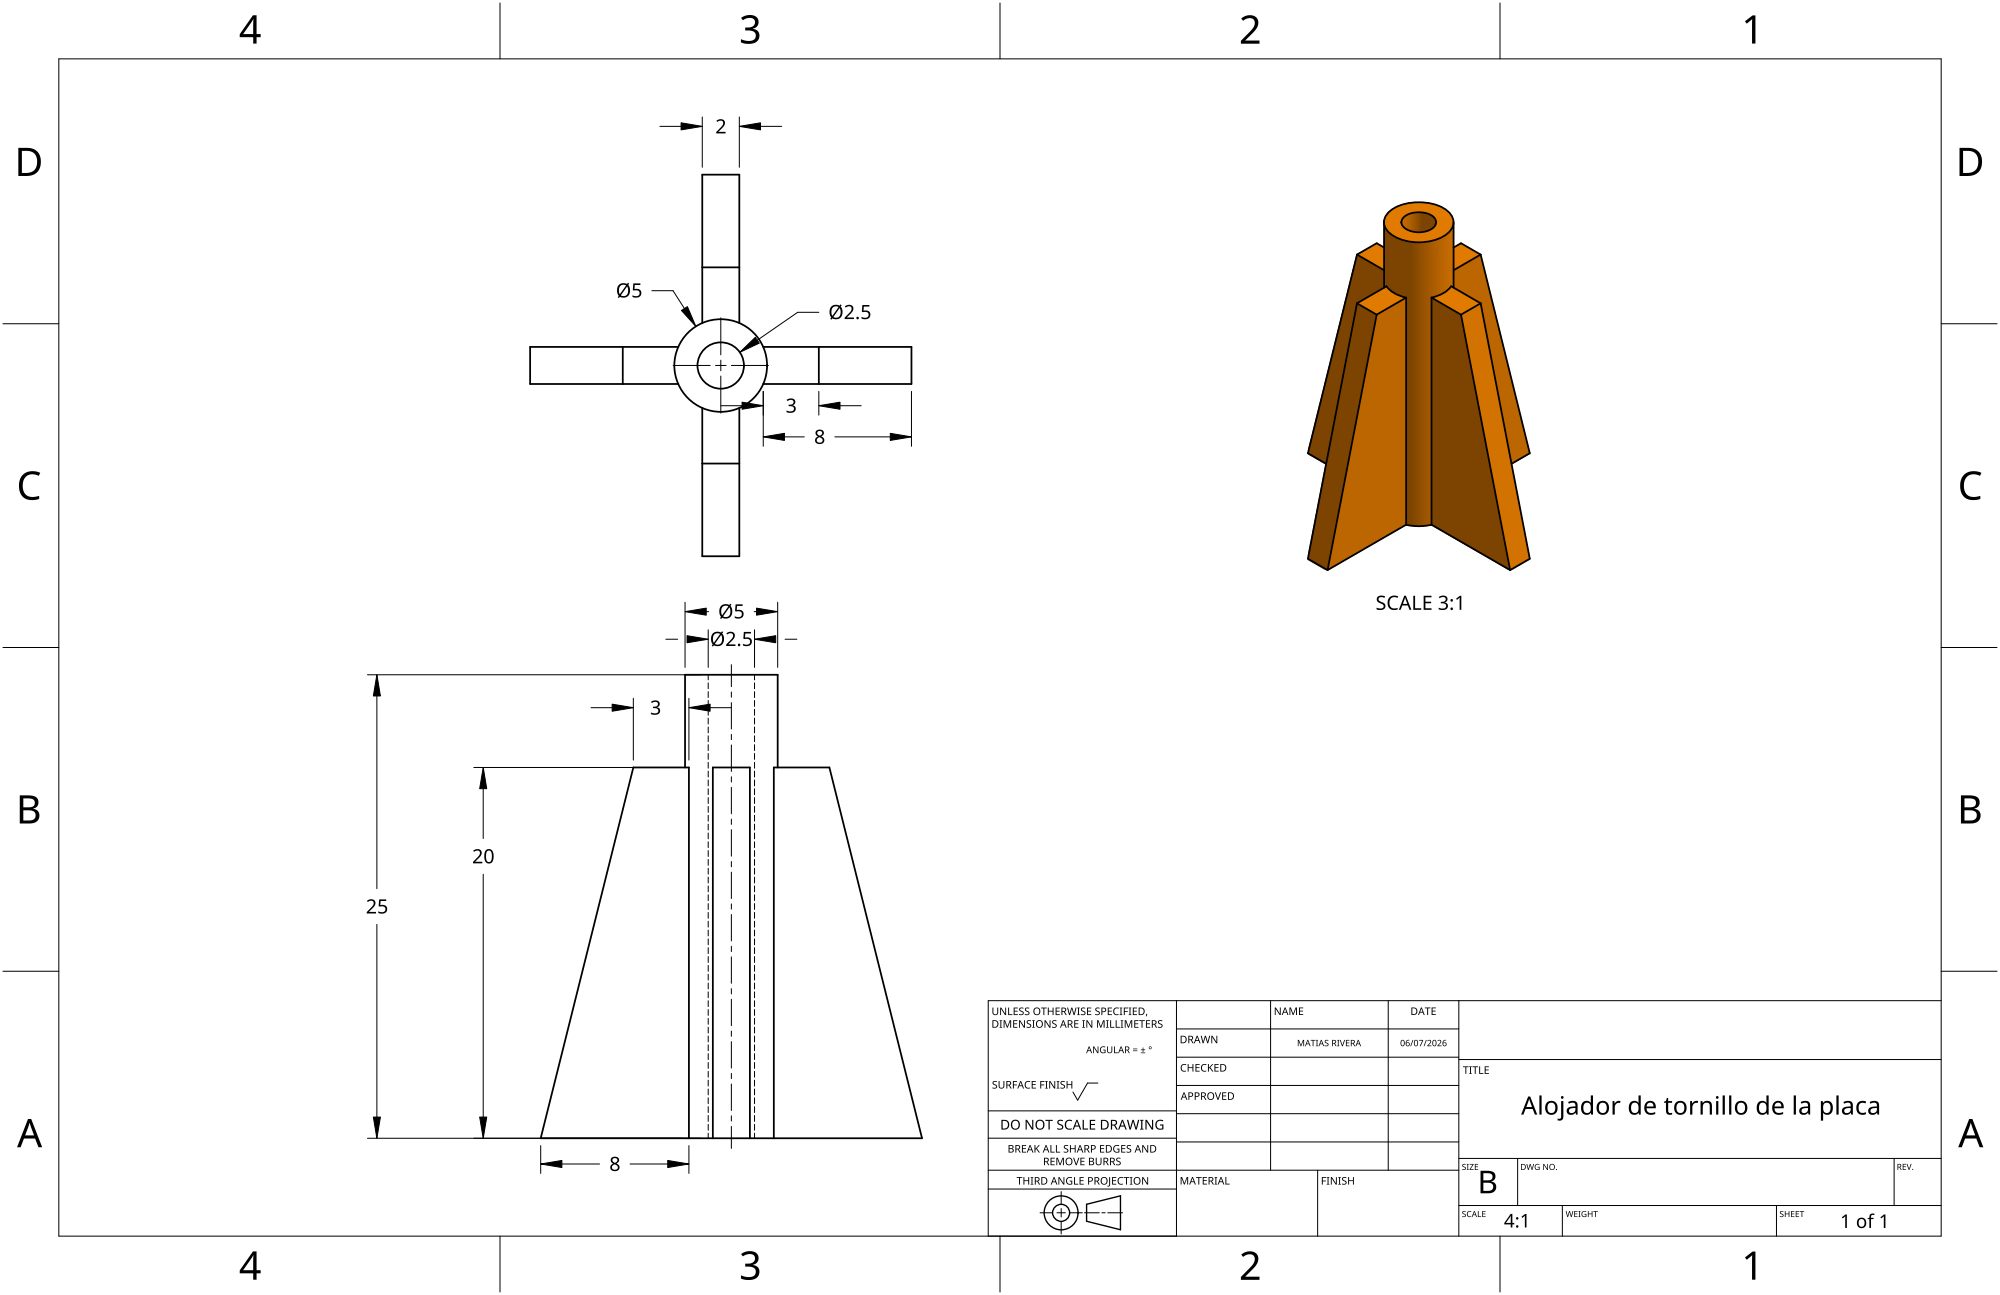
[picture p73: page 1]
