matiasrg/FdD_Equipo_04/Proyecto/MóduloMecánico/vfinal/Oneshape/Planos/Fijador de la tapa.pdf

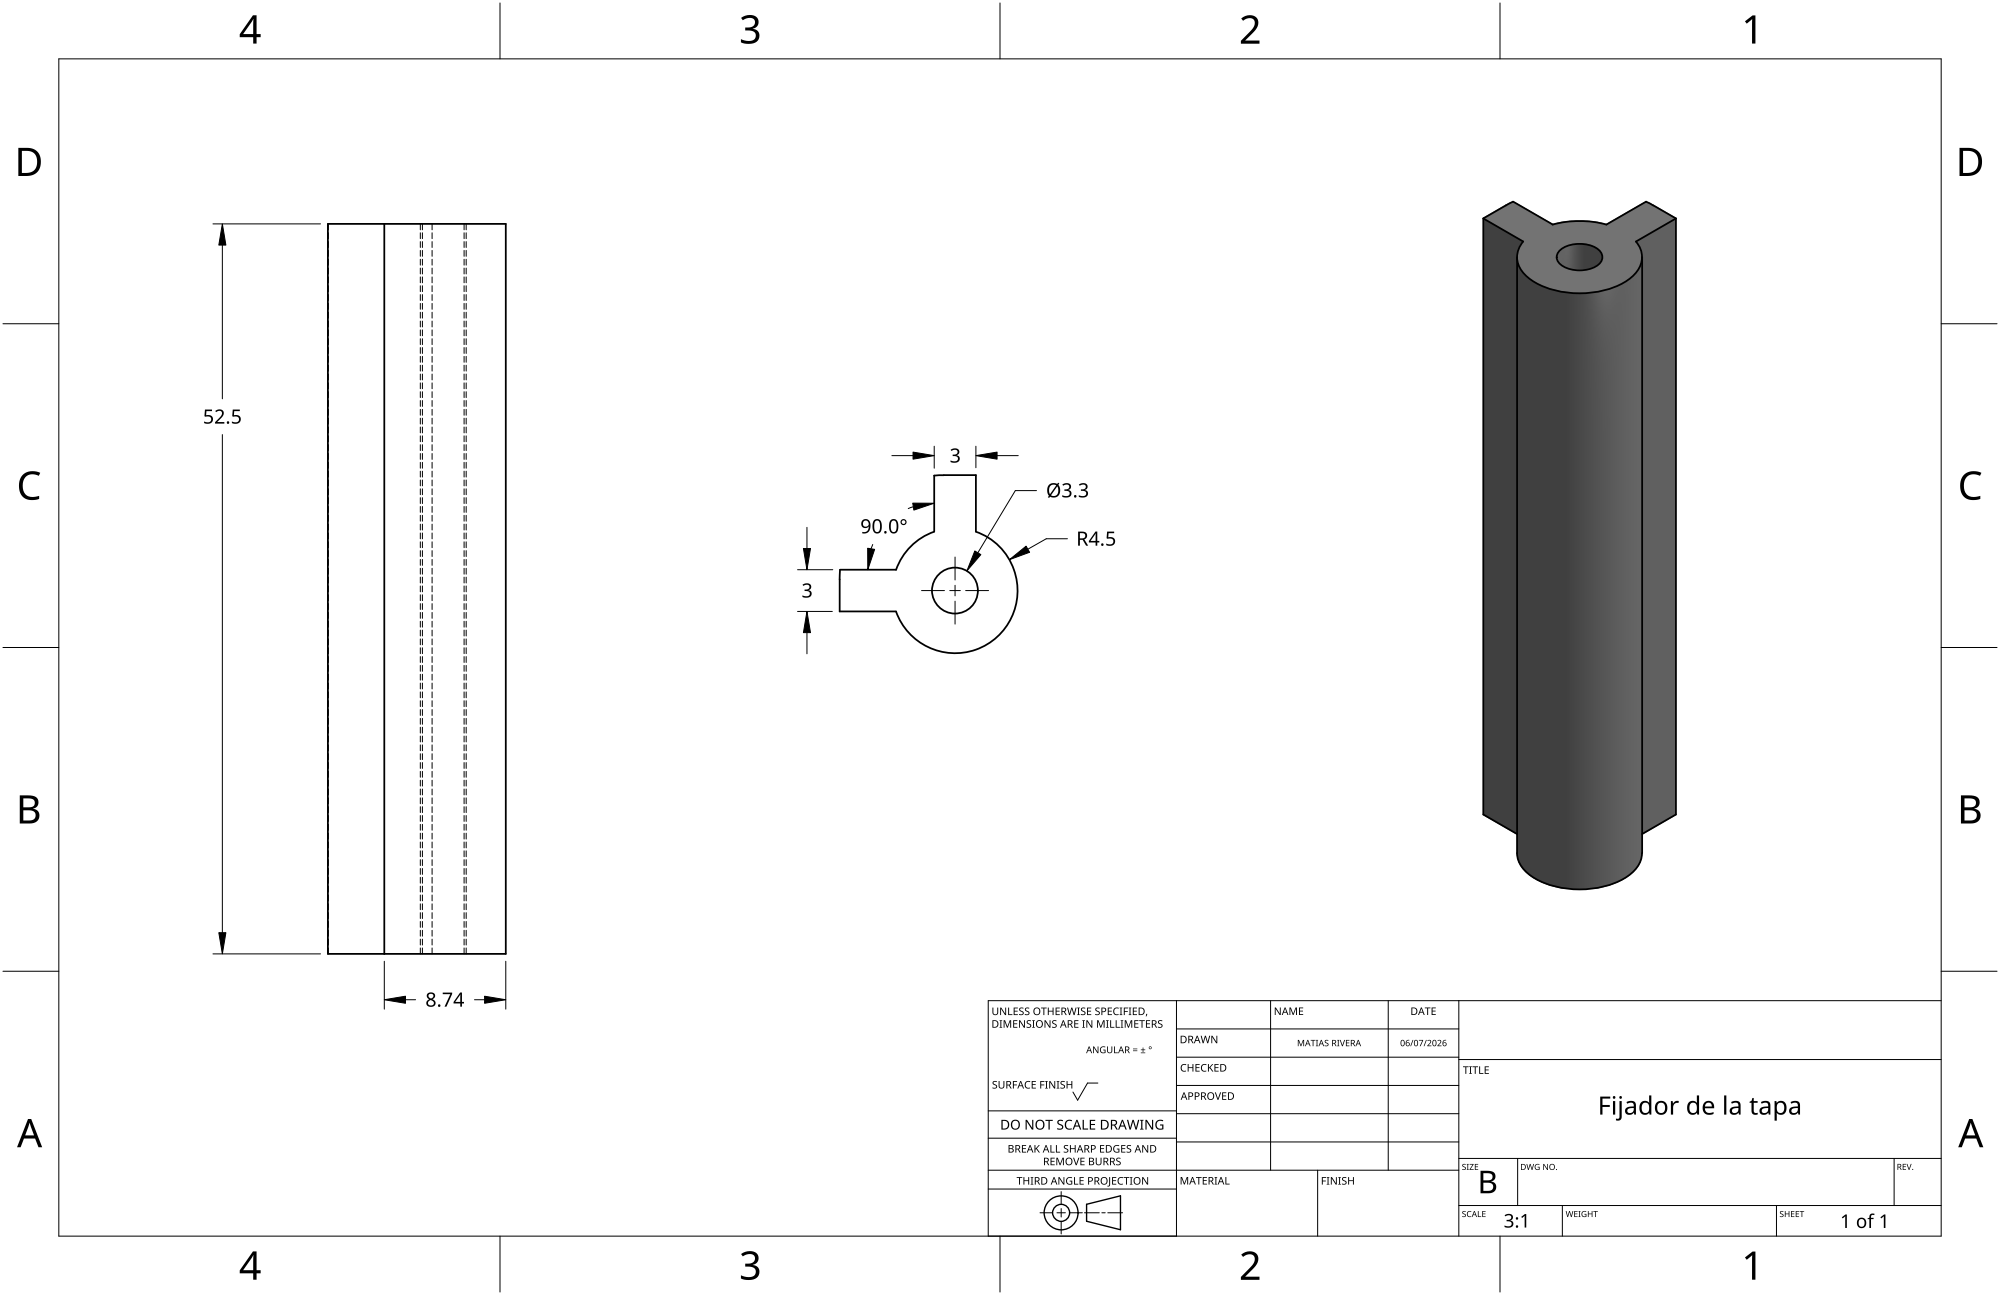
[picture p74: page 1]
