matiasrg/FdD_Equipo_04/Proyecto/MóduloMecánico/vfinal/Oneshape/Planos/Tapa de los sensores.pdf

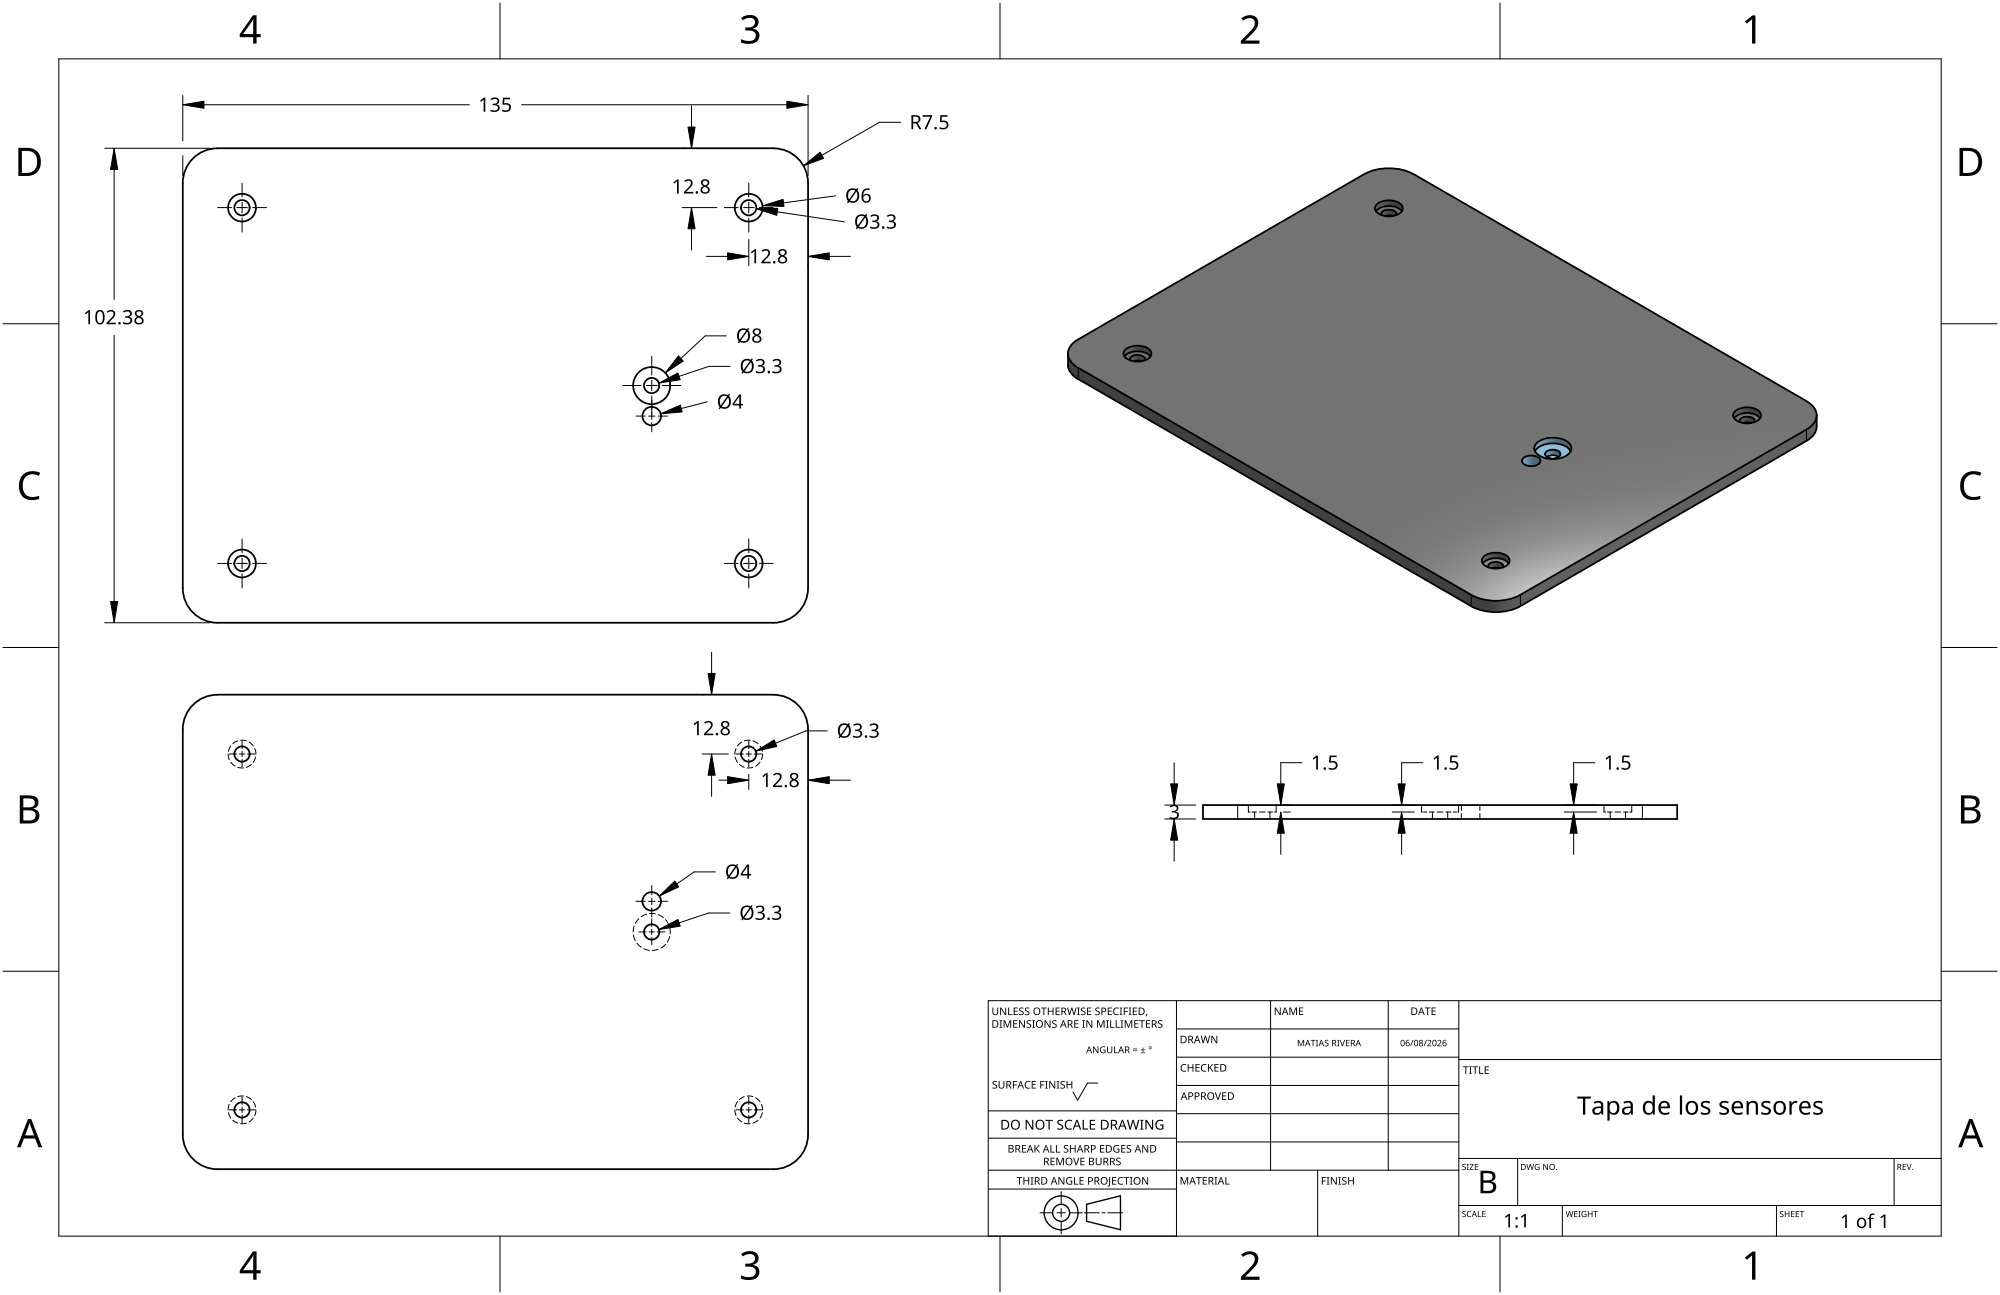
[picture p75: page 1]
