matiasrg/FdD_Equipo_04/Proyecto/MóduloMecánico/vfinal/Oneshape/Planos/Tapa del ESP32.pdf

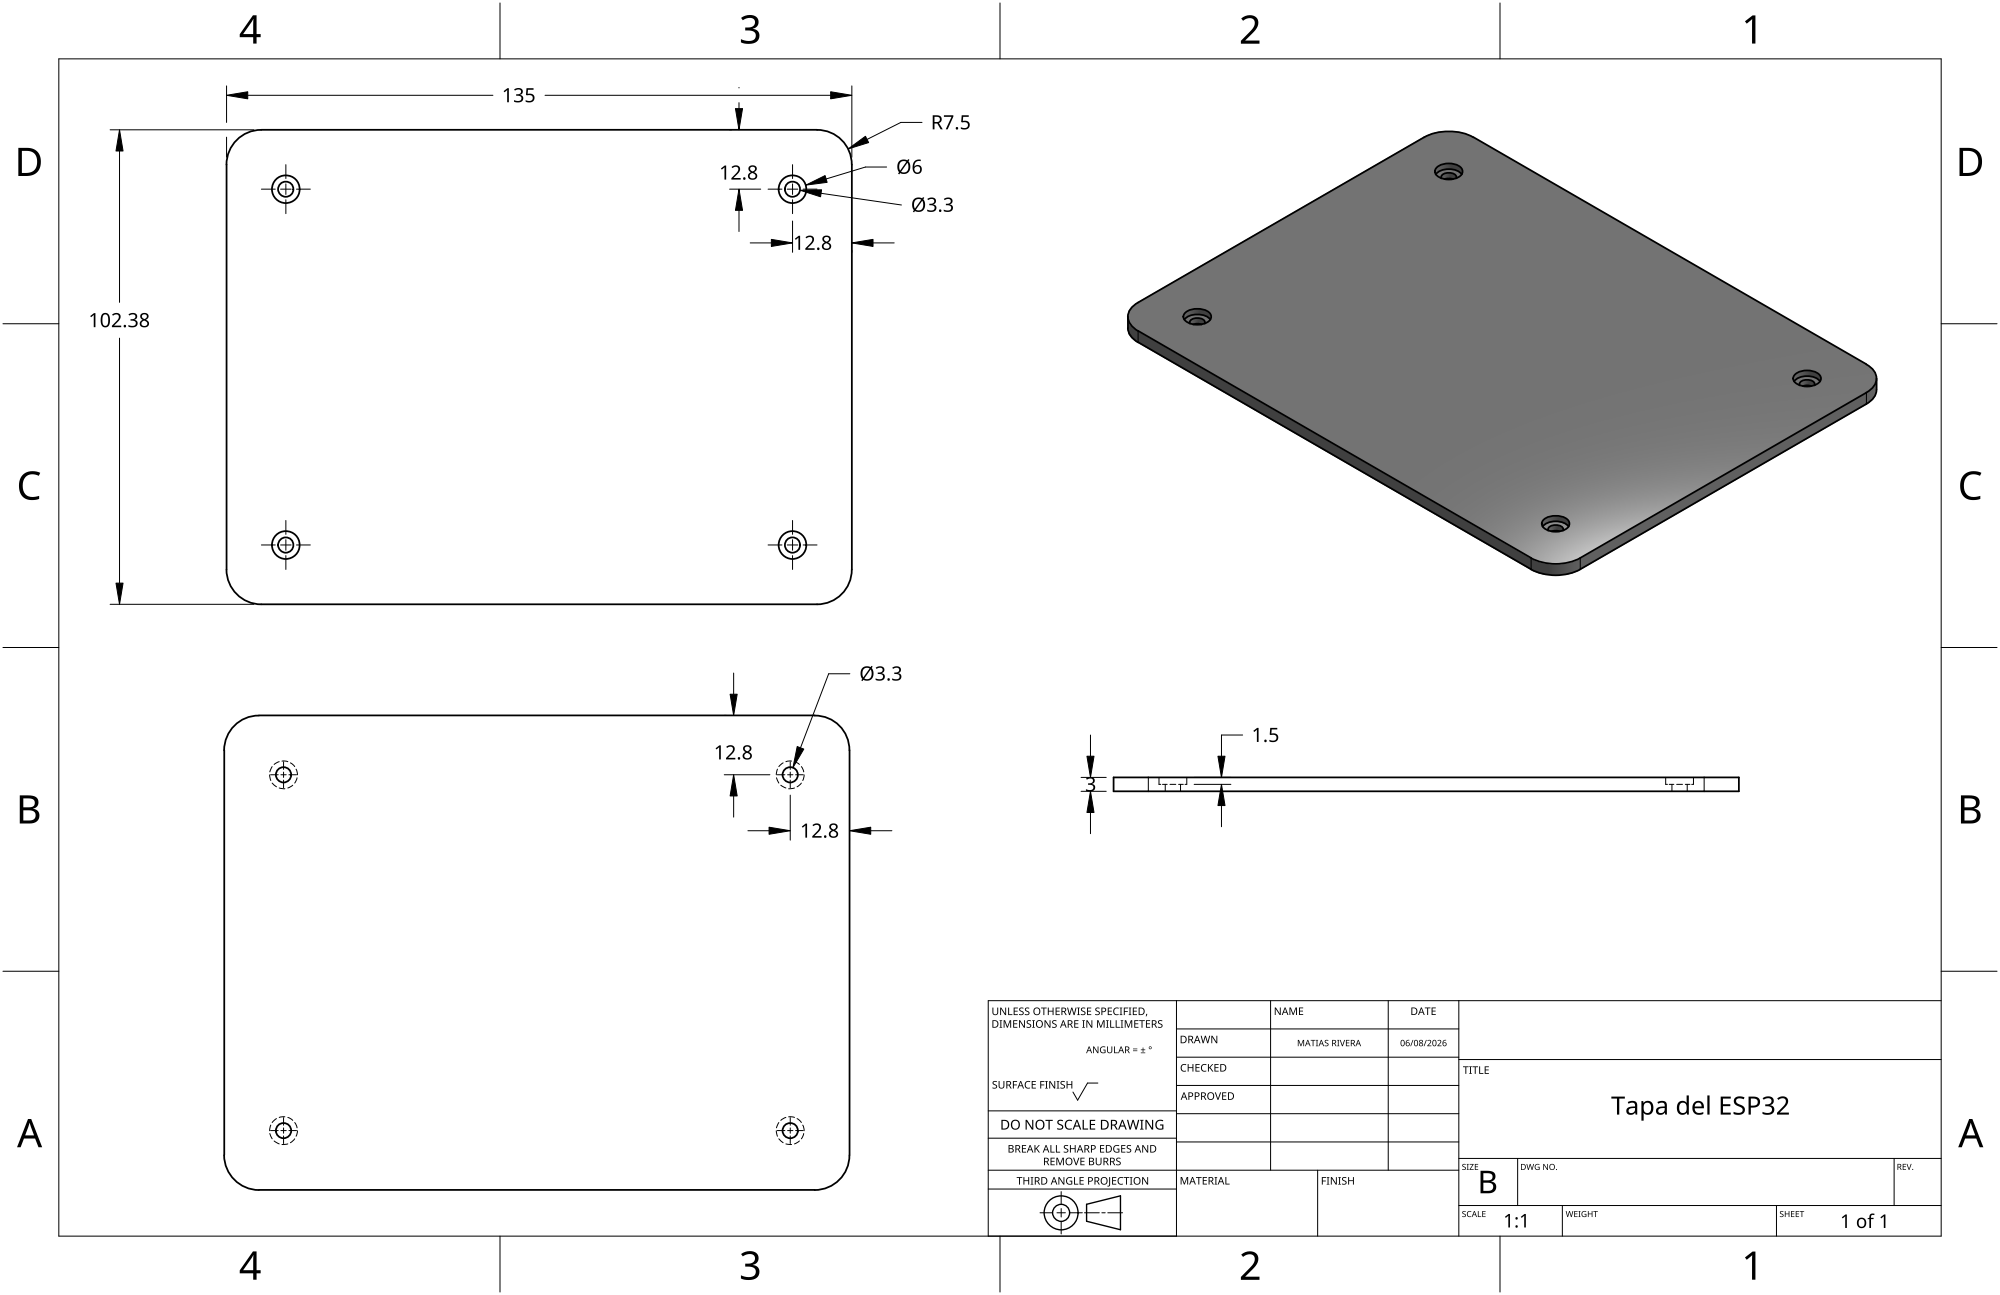
[picture p76: page 1]
